romainflcht/wibbly-wobbly-timey-wimey/3D_MODELS/front_face.stl

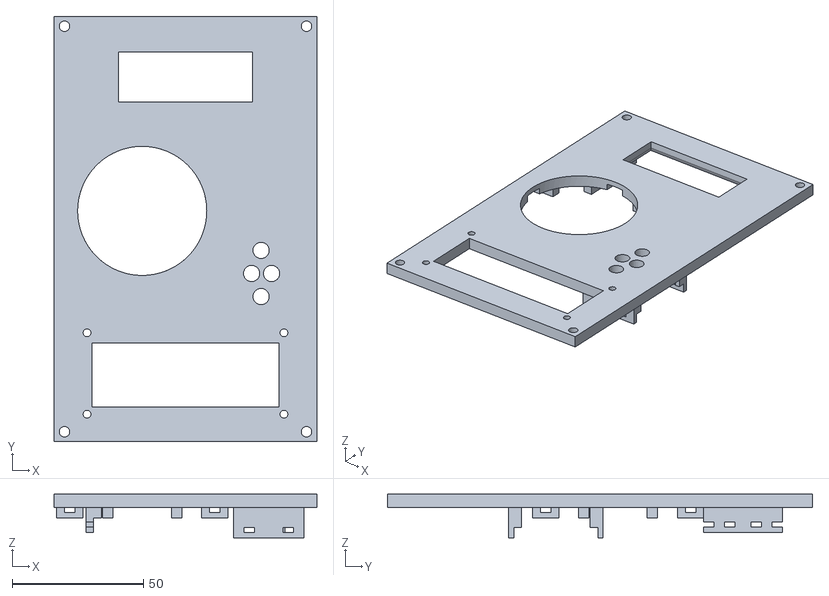
[picture p26: CAD file, 2024-01-29]
3D_MODELS/front_face.stl
100.2 x 162.0 x 16.7
