romainflcht/wibbly-wobbly-timey-wimey/3D_MODELS/clip.stl

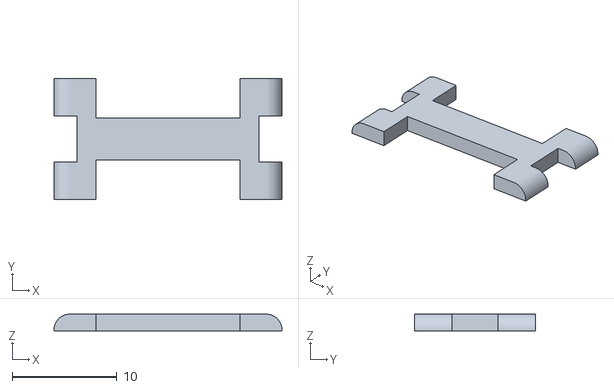
[picture p27: CAD file, 2024-01-29]
3D_MODELS/clip.stl
21.8 x 11.6 x 1.60
