romainflcht/wibbly-wobbly-timey-wimey/3D_MODELS/joystick_module.stl

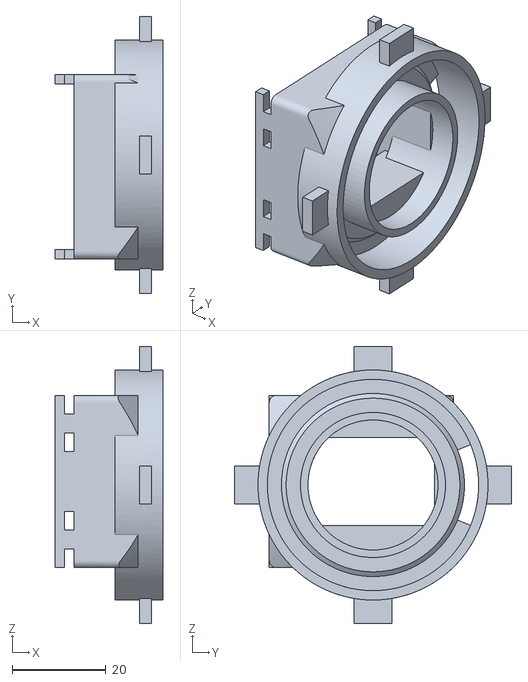
[picture p28: CAD file, 2024-01-29]
3D_MODELS/joystick_module.stl
23.0 x 59.0 x 59.0
