romainflcht/wibbly-wobbly-timey-wimey/3D_MODELS/alim_bar.stl

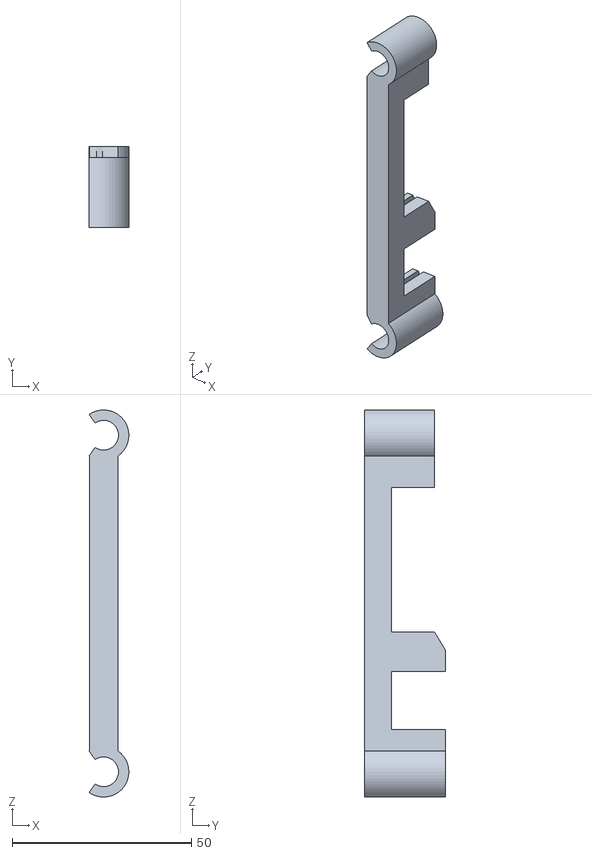
[picture p29: CAD file, 2024-01-29]
3D_MODELS/alim_bar.stl
11.1 x 22.5 x 108.0
