romainflcht/wibbly-wobbly-timey-wimey/3D_MODELS/button.stl

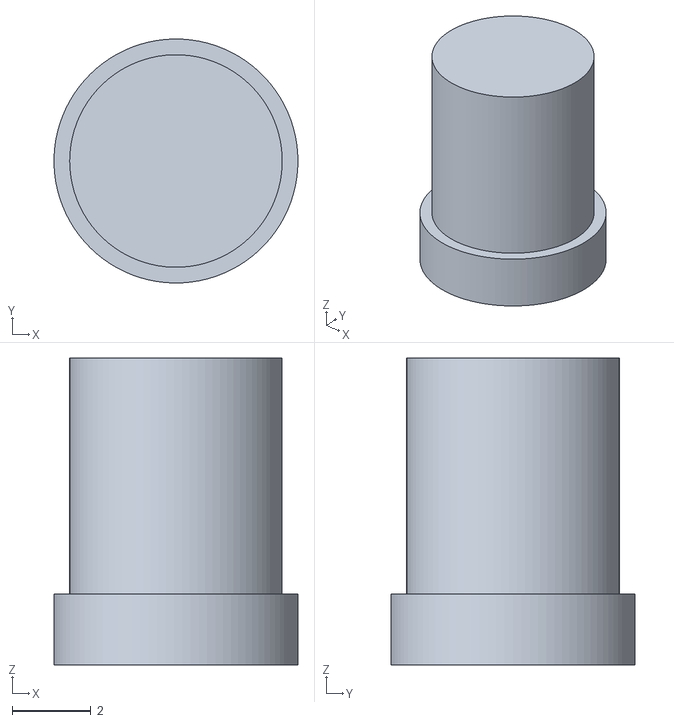
[picture p30: CAD file, 2024-01-29]
3D_MODELS/button.stl
6.20 x 6.20 x 7.80
