romainflcht/wibbly-wobbly-timey-wimey/3D_MODELS/battery_holder.stl

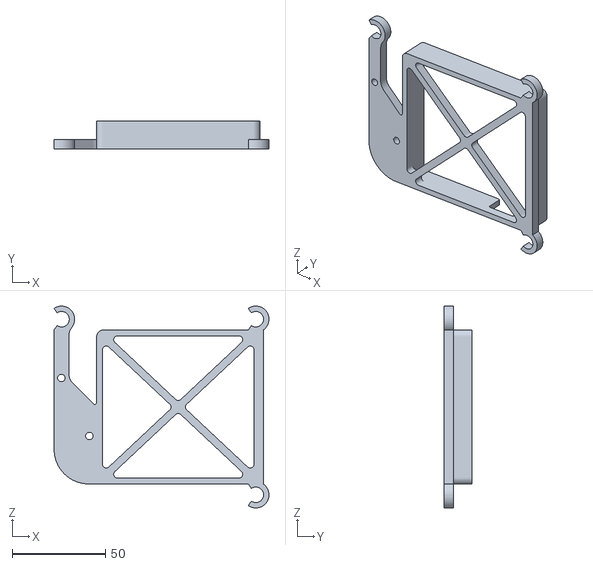
[picture p31: CAD file, 2024-01-29]
3D_MODELS/battery_holder.stl
115.0 x 15.0 x 108.0
