romainflcht/wibbly-wobbly-timey-wimey/3D_MODELS/joystick_clip.stl

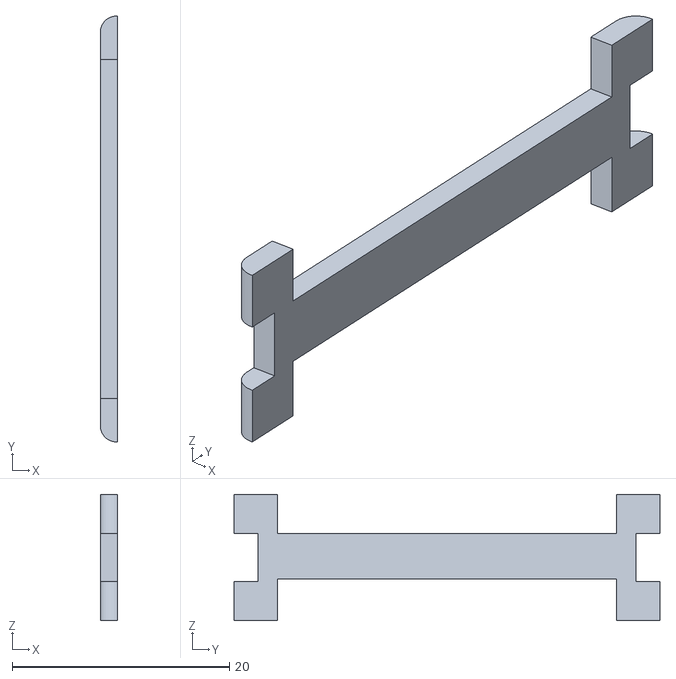
[picture p32: CAD file, 2024-01-29]
3D_MODELS/joystick_clip.stl
1.60 x 39.2 x 11.6
