romainflcht/wibbly-wobbly-timey-wimey/3D_MODELS/led_diffuser.stl

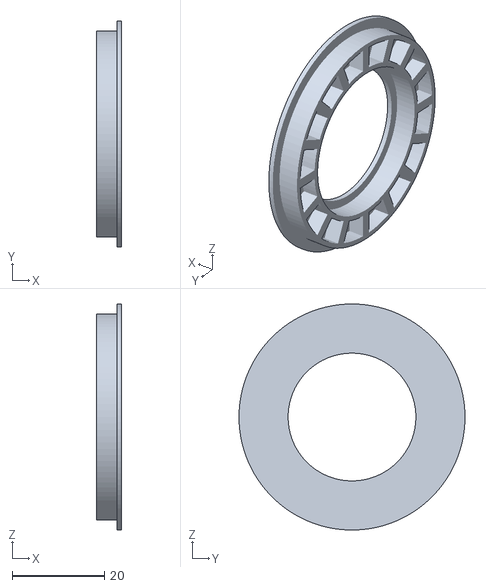
[picture p33: CAD file, 2024-01-29]
3D_MODELS/led_diffuser.stl
5.40 x 49.0 x 49.0
