romainflcht/wibbly-wobbly-timey-wimey/3D_MODELS/top_cover.stl

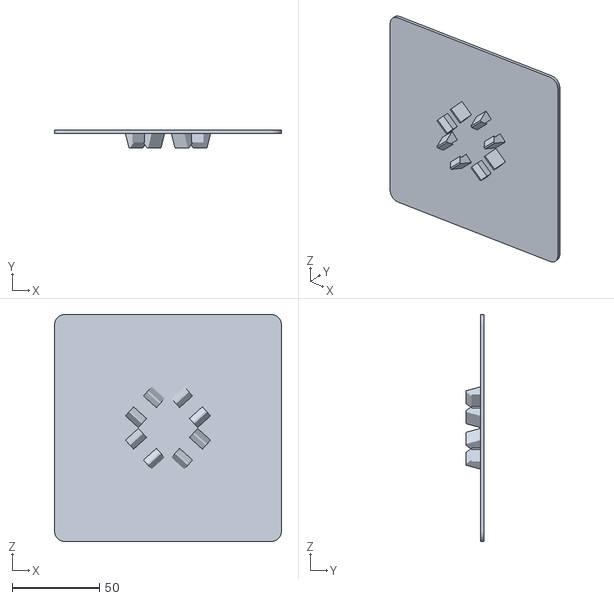
[picture p34: CAD file, 2024-01-29]
3D_MODELS/top_cover.stl
130.0 x 10.2 x 130.0
