romainflcht/wibbly-wobbly-timey-wimey/WIBBLY-WOBBLY-TIMEY-WIMEY-CODE/special_char.h

const byte offset_glyph[26][8] = {
  { 0x04, 0x0A, 0x11, 0x11, 0x0A, 0x04, 0x00, 0x04 },
  { 0x04, 0x0A, 0x11, 0x15, 0x0A, 0x00, 0x00, 0x00 },
  { 0x04, 0x0A, 0x11, 0x15, 0x0A, 0x00, 0x04, 0x02 },
  { 0x04, 0x0A, 0x11, 0x15, 0x0A, 0x00, 0x04, 0x0A },
  { 0x04, 0x0A, 0x11, 0x15, 0x0A, 0x04, 0x04, 0x00 },
  { 0x04, 0x0E, 0x1F, 0x1F, 0x0A, 0x00, 0x00, 0x00 },
  { 0x04, 0x0E, 0x15, 0x15, 0x0A, 0x00, 0x00, 0x00 },
  { 0x04, 0x0A, 0x1B, 0x1F, 0x0A, 0x00, 0x00, 0x00 },
  { 0x04, 0x0E, 0x15, 0x15, 0x0E, 0x04, 0x04, 0x04 },
  { 0x04, 0x0A, 0x11, 0x15, 0x0A, 0x04, 0x00, 0x00 },
  { 0x04, 0x0A, 0x11, 0x17, 0x0A, 0x04, 0x00, 0x00 },
  { 0x04, 0x0A, 0x11, 0x1F, 0x0A, 0x04, 0x00, 0x00 },
  { 0x04, 0x0E, 0x1B, 0x11, 0x0A, 0x04, 0x00, 0x00 },
  { 0x04, 0x0E, 0x11, 0x11, 0x0A, 0x04, 0x00, 0x00 },
  { 0x04, 0x0A, 0x11, 0x11, 0x0E, 0x04, 0x00, 0x00 },
  { 0x04, 0x0A, 0x1B, 0x11, 0x0A, 0x04, 0x00, 0x00 },
  { 0x04, 0x0E, 0x15, 0x15, 0x0E, 0x04, 0x00, 0x00 },
  { 0x04, 0x0A, 0x11, 0x15, 0x1B, 0x15, 0x0A, 0x00 },
  { 0x04, 0x0E, 0x1F, 0x1F, 0x11, 0x00, 0x00, 0x00 },
  { 0x04, 0x0A, 0x11, 0x15, 0x1B, 0x11, 0x00, 0x00 },
  { 0x04, 0x0A, 0x11, 0x11, 0x0A, 0x04, 0x04, 0x00 },
  { 0x04, 0x0E, 0x15, 0x15, 0x1B, 0x11, 0x00, 0x00 },
  { 0x04, 0x0A, 0x1B, 0x1F, 0x1B, 0x11, 0x00, 0x00 },
  { 0x04, 0x0A, 0x1B, 0x1B, 0x0A, 0x04, 0x0A, 0x04 },
  { 0x04, 0x0A, 0x1B, 0x1B, 0x0A, 0x04, 0x0B, 0x04 },
  { 0x04, 0x0A, 0x1B, 0x1B, 0x0A, 0x04, 0x1B, 0x04 }
};
